jnwajei22/raspberry-pi-nas-filesystem/hardware/pcb/kicad/raspberry_pi_nas_nvme.kicad_sch

## KiCad design hardware/pcb/kicad/raspberry_pi_nas_nvme.kicad_sch (2026-09-16)

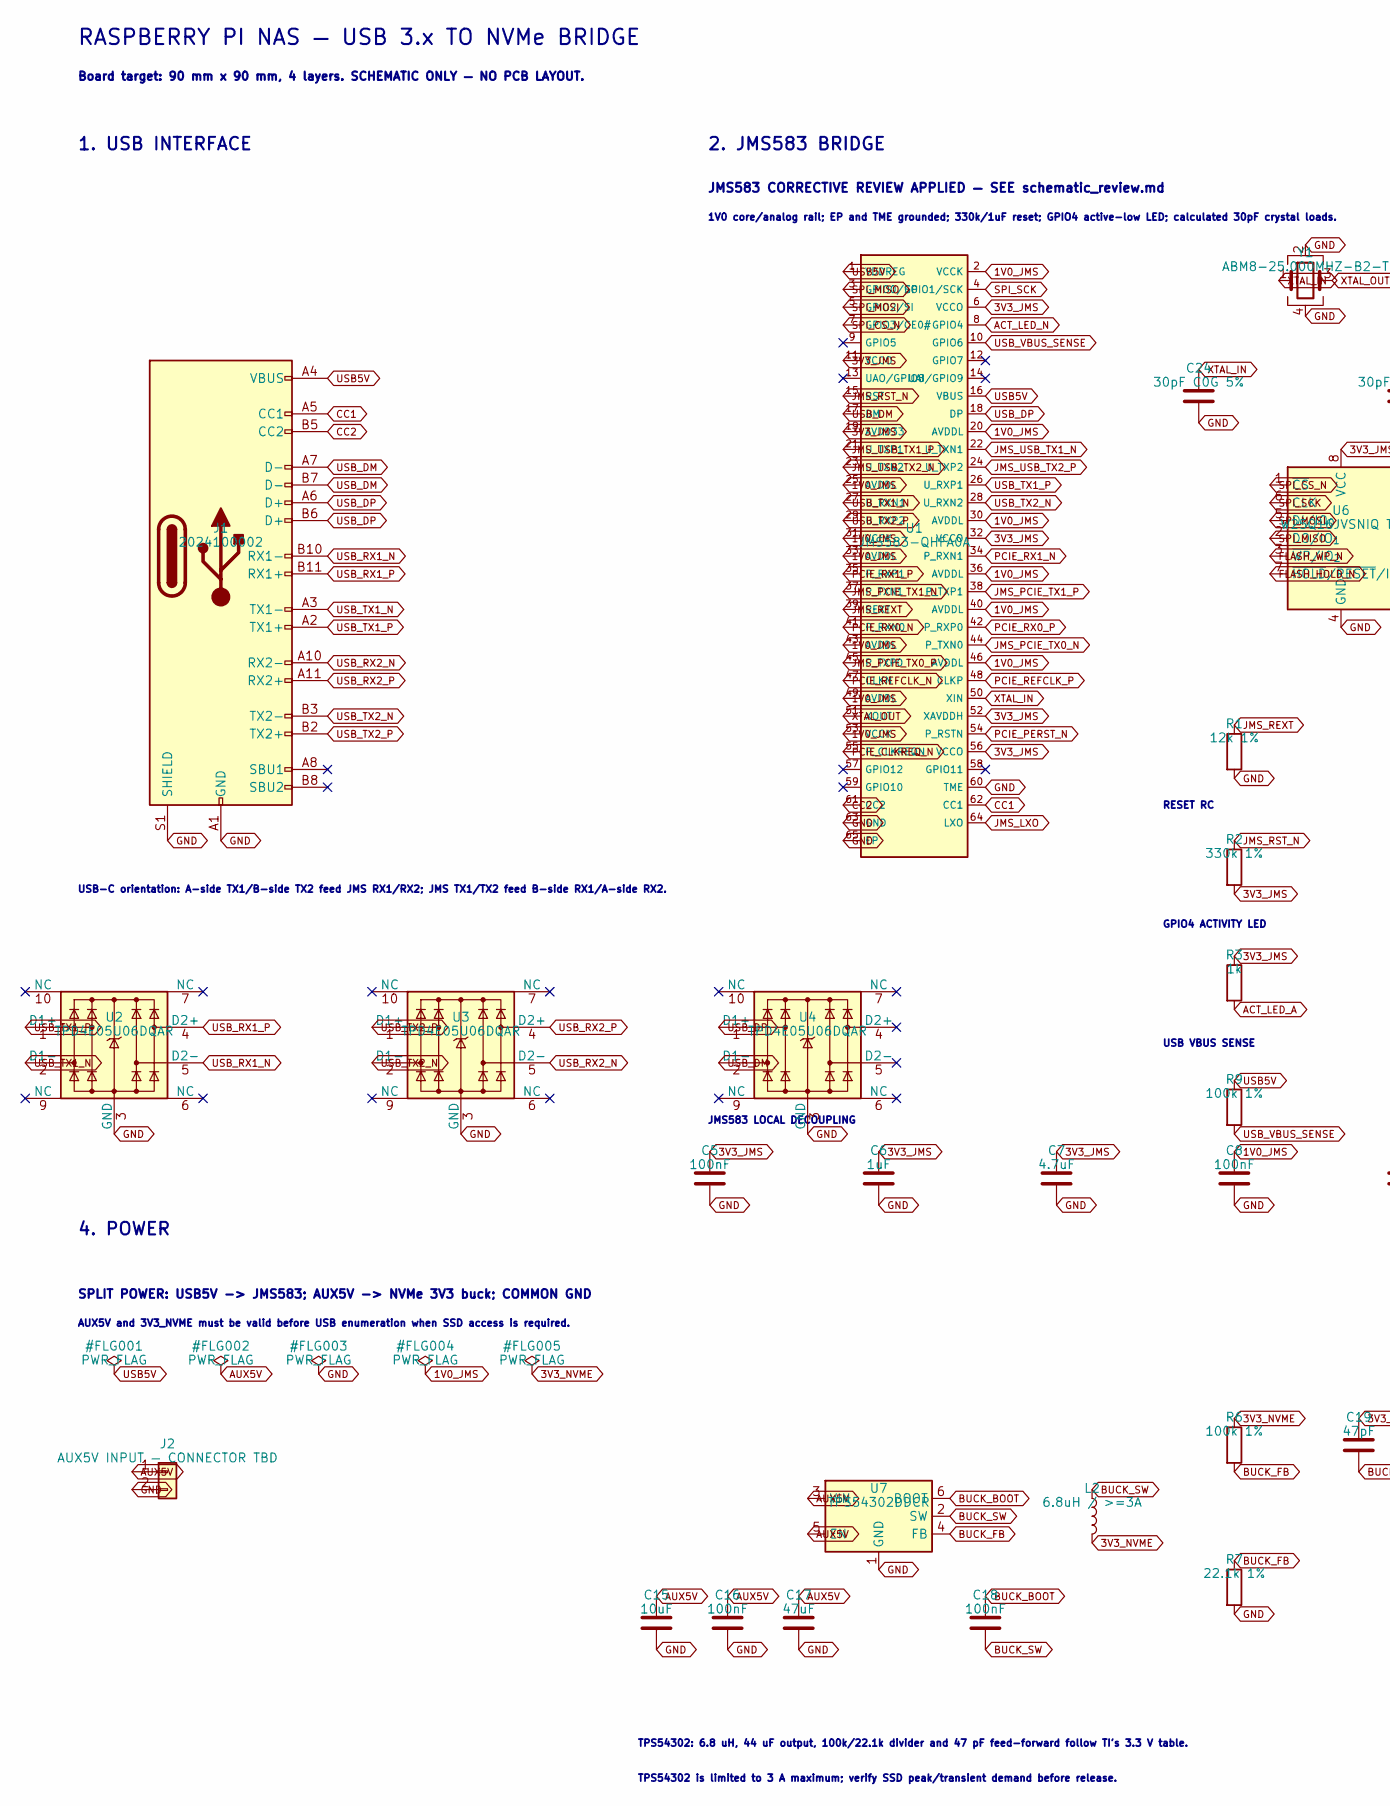
[picture p2: schematic raspberry_pi_nas_nvme.kicad_sch, part in row 1, column 1]

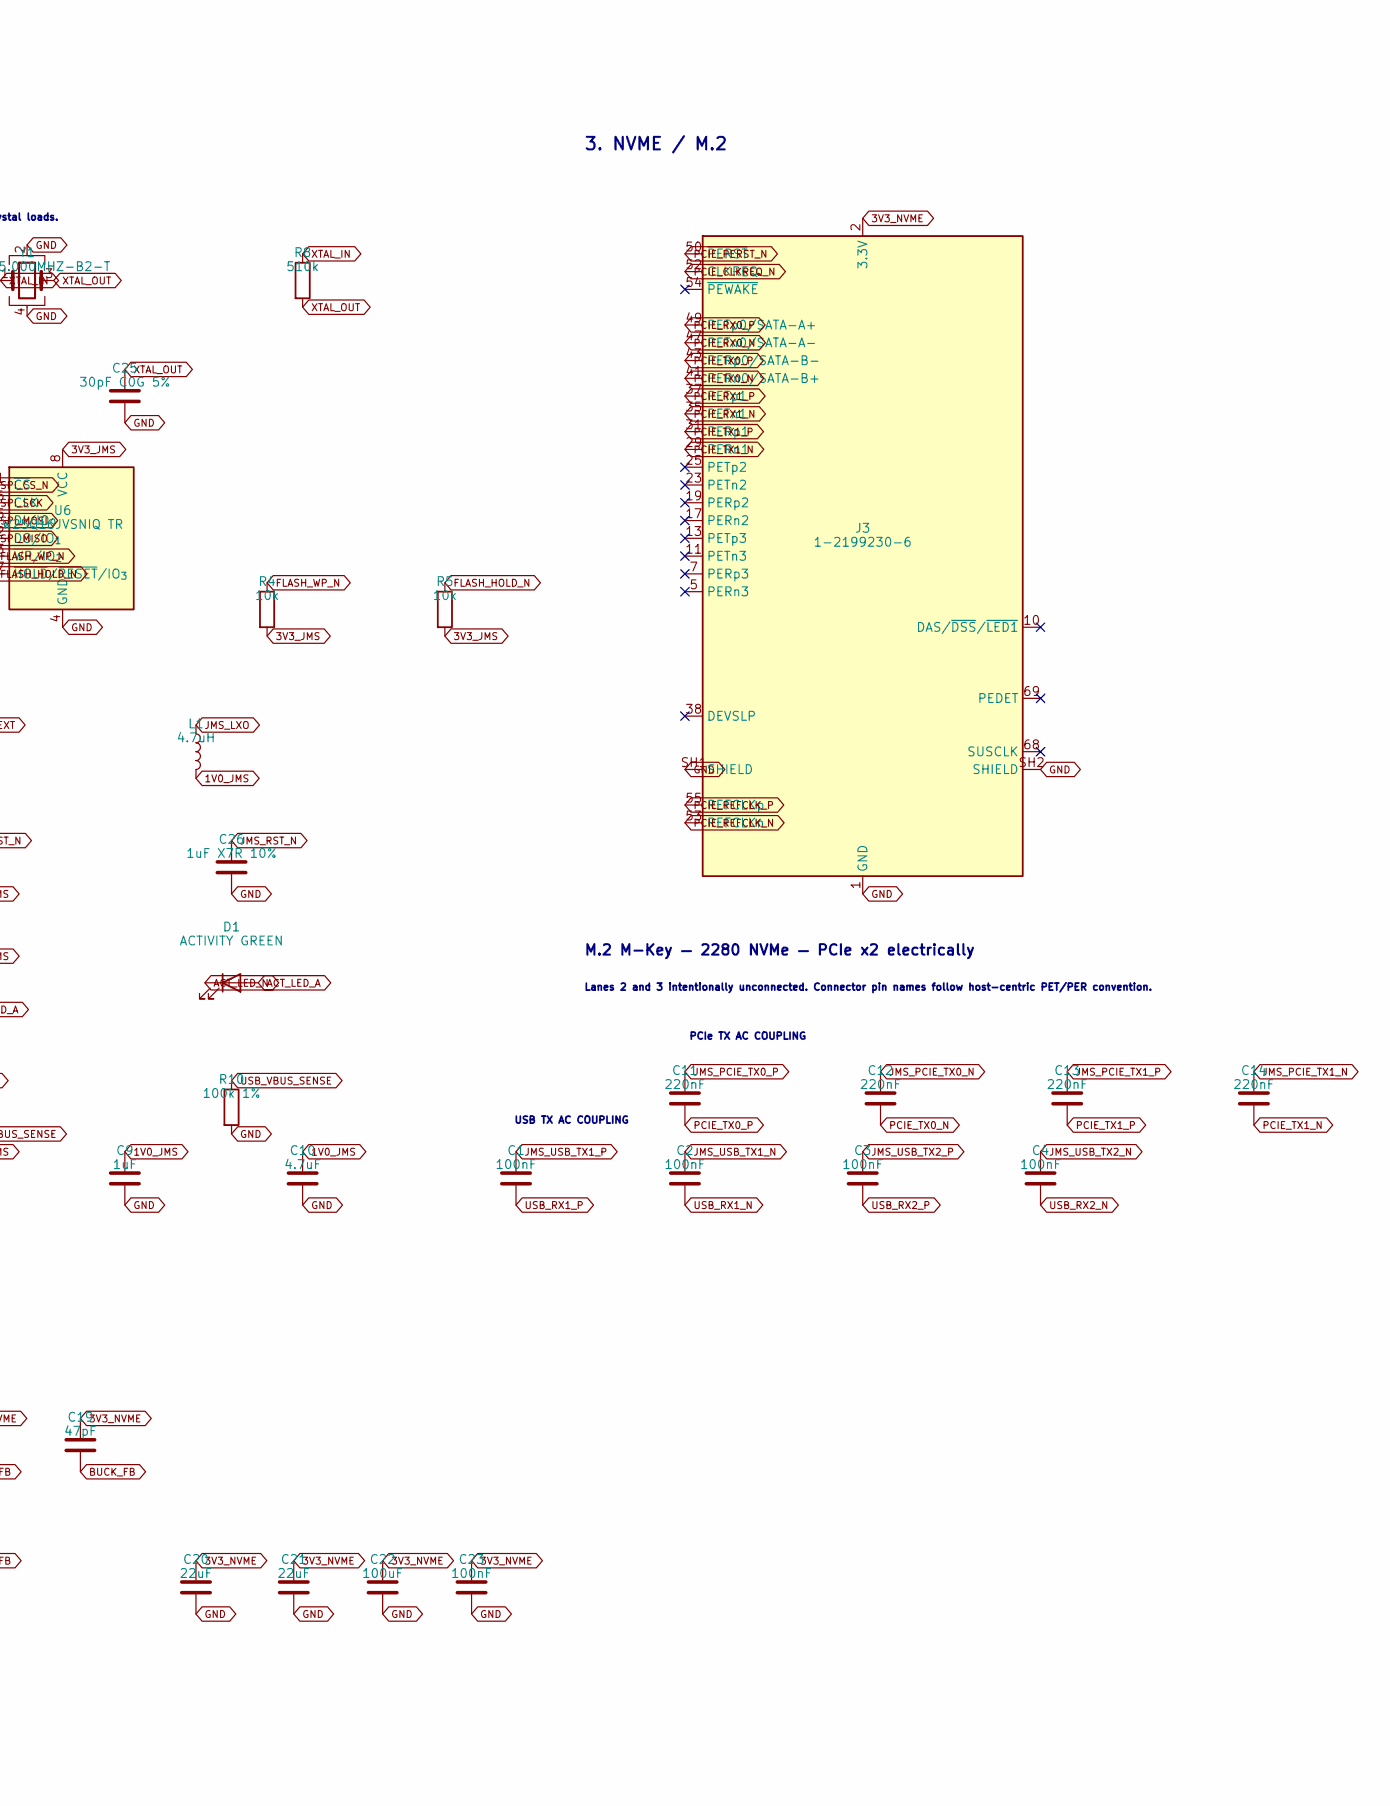
[picture p3: schematic raspberry_pi_nas_nvme.kicad_sch, part in row 1, column 2]

Parts:
C1, C2, C3, C4, C5, C8, C16, C18, C23: 100nF; C_0603_1608Metric_Pad1.08x0.95mm_HandSolder
C6, C9: 1uF; C_0603_1608Metric_Pad1.08x0.95mm_HandSolder
C7, C10: 4.7uF; C_0603_1608Metric_Pad1.08x0.95mm_HandSolder
C11, C12, C13, C14: 220nF; C_0603_1608Metric_Pad1.08x0.95mm_HandSolder
C15: 10uF; C_1210_3225Metric_Pad1.33x2.70mm_HandSolder
C17: 47uF; C_1210_3225Metric_Pad1.33x2.70mm_HandSolder
C19: 47pF; C_0603_1608Metric_Pad1.08x0.95mm_HandSolder
C20, C21: 22uF; C_1210_3225Metric_Pad1.33x2.70mm_HandSolder
C22: 100uF; C_1210_3225Metric_Pad1.33x2.70mm_HandSolder
C24, C25: 30pF C0G 5%; C_0603_1608Metric_Pad1.08x0.95mm_HandSolder
C26: 1uF X7R 10%; C_0603_1608Metric_Pad1.08x0.95mm_HandSolder
D1: ACTIVITY GREEN; LED_0603_1608Metric_Pad1.05x0.95mm_HandSolder
J1: 2024100002; Molex_2024100002
J2: AUX5V INPUT — CONNECTOR TBD
J3: 1-2199230-6; TE_1-2199230-6_M2_M_Key
L1: 4.7uH; L_1210_3225Metric_Pad1.42x2.65mm_HandSolder
L2: 6.8uH / >=3A; L_1210_3225Metric_Pad1.42x2.65mm_HandSolder
R1: 12k 1%; R_0603_1608Metric_Pad0.98x0.95mm_HandSolder
R2: 330k 1%; R_0603_1608Metric_Pad0.98x0.95mm_HandSolder
R3: 1k; R_0603_1608Metric_Pad0.98x0.95mm_HandSolder
R4, R5: 10k; R_0603_1608Metric_Pad0.98x0.95mm_HandSolder
R6, R9, R10: 100k 1%; R_0603_1608Metric_Pad0.98x0.95mm_HandSolder
R7: 22.1k 1%; R_0603_1608Metric_Pad0.98x0.95mm_HandSolder
R8: 510k; R_0603_1608Metric_Pad0.98x0.95mm_HandSolder
U1: JMS583-QHFA0A; JMicron_JMS583-QHFA0A
U2, U3, U4: TPD4E05U06DQAR; TPD4E05U06DQAR_DQA0010A
U6: W25Q16JVSNIQ TR; Winbond_W25Q16JVSNIQ_SOIC8_150mil
U7: TPS54302DDCR; TPS54302DDCR_DDC0006A
Y1: ABM8-25.000MHZ-B2-T; Abracon_ABM8-25.000MHZ-B2-T

Connections:
1V0_JMS: C8.1, C9.1, C10.1, L1.2, U1.2 (VCCK), U1.20 (AVDDL), U1.25 (AVDDL), U1.30 (AVDDL), U1.31 (VCCK), U1.33 (AVDDL), U1.36 (AVDDL), U1.40 (AVDDL), U1.43 (AVDDL), U1.46 (AVDDL), U1.49 (AVDDL), U1.53 (VCCK)
3V3_JMS: C5.1, C6.1, C7.1, R2.2, R3.1, R4.2, R5.2, U1.6 (VCCO), U1.11 (VCCO), U1.19 (AVDD33), U1.32 (VCCO), U1.52 (XAVDDH), U1.56 (VCCO), U6.8 (VCC)
3V3_NVME: C19.1, C20.1, C21.1, C22.1, C23.1, J3.2 (3.3V), J3.4 (3.3V), J3.12 (3.3V), J3.14 (3.3V), J3.16 (3.3V), J3.18 (3.3V), J3.70 (3.3V), J3.72 (3.3V), J3.74 (3.3V), L2.2, R6.1
ACT_LED_A: D1.2 (A), R3.2
ACT_LED_N: D1.1 (K), U1.8 (GPIO4)
AUX5V: C15.1, C16.1, C17.1, J2.1, U7.3 (VIN), U7.5 (EN)
BUCK_BOOT: C18.1, U7.6 (BOOT)
BUCK_FB: C19.2, R6.2, R7.1, U7.4 (FB)
BUCK_SW: C18.2, L2.1, U7.2 (SW)
CC1: J1.A5 (CC1), U1.62 (CC1)
CC2: J1.B5 (CC2), U1.61 (CC2)
FLASH_HOLD_N: R5.1, U6.7 (~HOLD/~RESET/IO_{3})
FLASH_WP_N: R4.1, U6.3 (~WP/IO_{2})
GND: C5.2, C6.2, C7.2, C8.2, C9.2, C10.2, C15.2, C16.2, C17.2, C20.2, C21.2, C22.2, C23.2, C24.2, C25.2, C26.2, J1.A1 (GND), J1.A12 (GND), J1.B1 (GND), J1.B12 (GND), J1.S1 (SHIELD), J2.2, J3.1 (GND), J3.3 (GND), J3.9 (GND), J3.15 (GND), J3.21 (GND), J3.27 (GND), J3.33 (GND), J3.39 (GND), J3.45 (GND), J3.51 (GND), J3.57 (GND), J3.71 (GND), J3.73 (GND), J3.75 (GND), J3.SH1 (SHIELD), J3.SH2 (SHIELD), R1.2, R7.2, R10.2, U1.60 (TME), U1.63 (GND), U1.65 (EP), U2.3 (GND), U2.8 (GND), U3.3 (GND), U3.8 (GND), U4.3 (GND), U4.8 (GND), U6.4 (GND), U7.1 (GND), Y1.2, Y1.4
JMS_LXO: L1.1, U1.64 (LXO)
JMS_PCIE_TX0_N: C12.1, U1.44 (P_TXN0)
JMS_PCIE_TX0_P: C11.1, U1.45 (P_TXP0)
JMS_PCIE_TX1_N: C14.1, U1.37 (P_TXN1)
JMS_PCIE_TX1_P: C13.1, U1.38 (P_TXP1)
JMS_REXT: R1.1, U1.39 (REXT)
JMS_RST_N: C26.1, R2.1, U1.15 (RST)
JMS_USB_TX1_N: C2.1, U1.22 (U_TXN1)
JMS_USB_TX1_P: C1.1, U1.21 (U_TXP1)
JMS_USB_TX2_N: C4.1, U1.23 (U_TXN2)
JMS_USB_TX2_P: C3.1, U1.24 (U_TXP2)
PCIE_CLKREQ_N: J3.52 (~CLKREQ), U1.55 (P_CLKREQN)
PCIE_PERST_N: J3.50 (~PERST), U1.54 (P_RSTN)
PCIE_REFCLK_N: J3.53 (REFCLKn), U1.47 (CLKN)
PCIE_REFCLK_P: J3.55 (REFCLKp), U1.48 (CLKP)
PCIE_RX0_N: J3.47 (PETn0/SATA-A-), U1.41 (P_RXN0)
PCIE_RX0_P: J3.49 (PETp0/SATA-A+), U1.42 (P_RXP0)
PCIE_RX1_N: J3.35 (PETn1), U1.34 (P_RXN1)
PCIE_RX1_P: J3.37 (PETp1), U1.35 (P_RXP1)
PCIE_TX0_N: C12.2, J3.41 (PERn0/SATA-B+)
PCIE_TX0_P: C11.2, J3.43 (PERp0/SATA-B-)
PCIE_TX1_N: C14.2, J3.29 (PERn1)
PCIE_TX1_P: C13.2, J3.31 (PERp1)
SPI_CS_N: U1.7 (GPIO3/CE0#), U6.1 (~CS)
SPI_MISO: U1.3 (GPIO0/SO), U6.2 (DO/IO_{1})
SPI_MOSI: U1.5 (GPIO2/SI), U6.5 (DI/IO_{0})
SPI_SCK: U1.4 (GPIO1/SCK), U6.6 (CLK)
USB5V: J1.A4 (VBUS), J1.A9 (VBUS), J1.B4 (VBUS), J1.B9 (VBUS), R9.1, U1.1 (VDDREG), U1.16 (VBUS)
USB_DM: J1.A7 (D-), J1.B7 (D-), U1.17 (DM), U4.2 (D1-)
USB_DP: J1.A6 (D+), J1.B6 (D+), U1.18 (DP), U4.1 (D1+)
USB_RX1_N: C2.2, J1.B10 (RX1-), U2.5 (D2-)
USB_RX1_P: C1.2, J1.B11 (RX1+), U2.4 (D2+)
USB_RX2_N: C4.2, J1.A10 (RX2-), U3.5 (D2-)
USB_RX2_P: C3.2, J1.A11 (RX2+), U3.4 (D2+)
USB_TX1_N: J1.A3 (TX1-), U1.27 (U_RXN1), U2.2 (D1-)
USB_TX1_P: J1.A2 (TX1+), U1.26 (U_RXP1), U2.1 (D1+)
USB_TX2_N: J1.B3 (TX2-), U1.28 (U_RXN2), U3.2 (D1-)
USB_TX2_P: J1.B2 (TX2+), U1.29 (U_RXP2), U3.1 (D1+)
USB_VBUS_SENSE: R9.2, R10.1, U1.10 (GPIO6)
XTAL_IN: C24.1, R8.1, U1.50 (XIN), Y1.1
XTAL_OUT: C25.1, R8.2, U1.51 (XOUT), Y1.3

Notes on the sheet:
RASPBERRY PI NAS — USB 3.x TO NVMe BRIDGE
Board target: 90 mm x 90 mm, 4 layers. SCHEMATIC ONLY — NO PCB LAYOUT.
1. USB INTERFACE
2. JMS583 BRIDGE
3. NVME / M.2
4. POWER
RESET RC
GPIO4 ACTIVITY LED
USB VBUS SENSE
JMS583 LOCAL DECOUPLING
USB TX AC COUPLING
JMS583 CORRECTIVE REVIEW APPLIED — SEE schematic_review.md
1V0 core/analog rail; EP and TME grounded; 330k/1uF reset; GPIO4 active-low LED; calculated 30pF crystal loads.
USB-C orientation: A-side TX1/B-side TX2 feed JMS RX1/RX2; JMS TX1/TX2 feed B-side RX1/A-side RX2.
M.2 M-Key — 2280 NVMe — PCIe x2 electrically
Lanes 2 and 3 intentionally unconnected. Connector pin names follow host-centric PET/PER convention.
PCIe TX AC COUPLING
SPLIT POWER: USB5V -> JMS583; AUX5V -> NVMe 3V3 buck; COMMON GND
AUX5V and 3V3_NVME must be valid before USB enumeration when SSD access is required.
TPS54302: 6.8 uH, 44 uF output, 100k/22.1k divider and 47 pF feed-forward follow TI's 3.3 V table.
TPS54302 is limited to 3 A maximum; verify SSD peak/transient demand before release.
